AniIOT/Foldable_Robotics_Project/04_Software/05_Markdown/Gallery.md

# Gallery

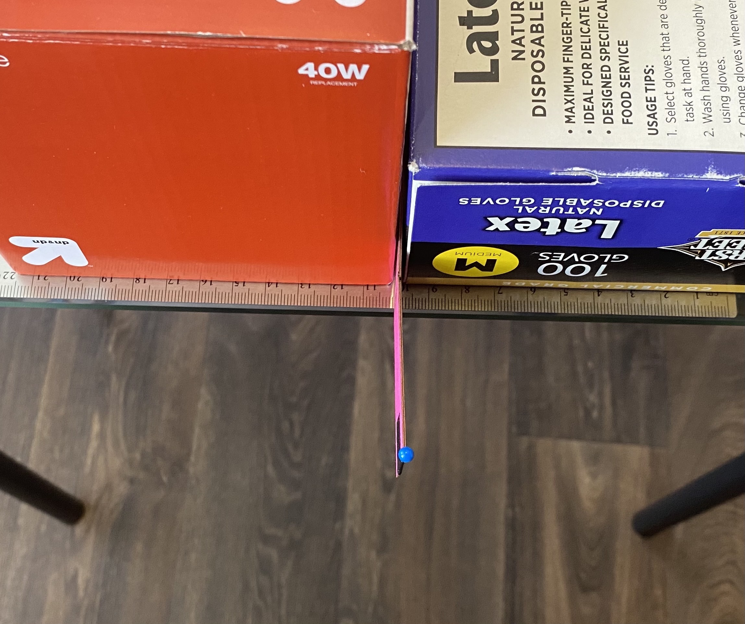
[picture p22: 04_Software/03_Anson/Damping_test_1.jpg]
damping_test_1


**Fig. 1: Damping test 1**

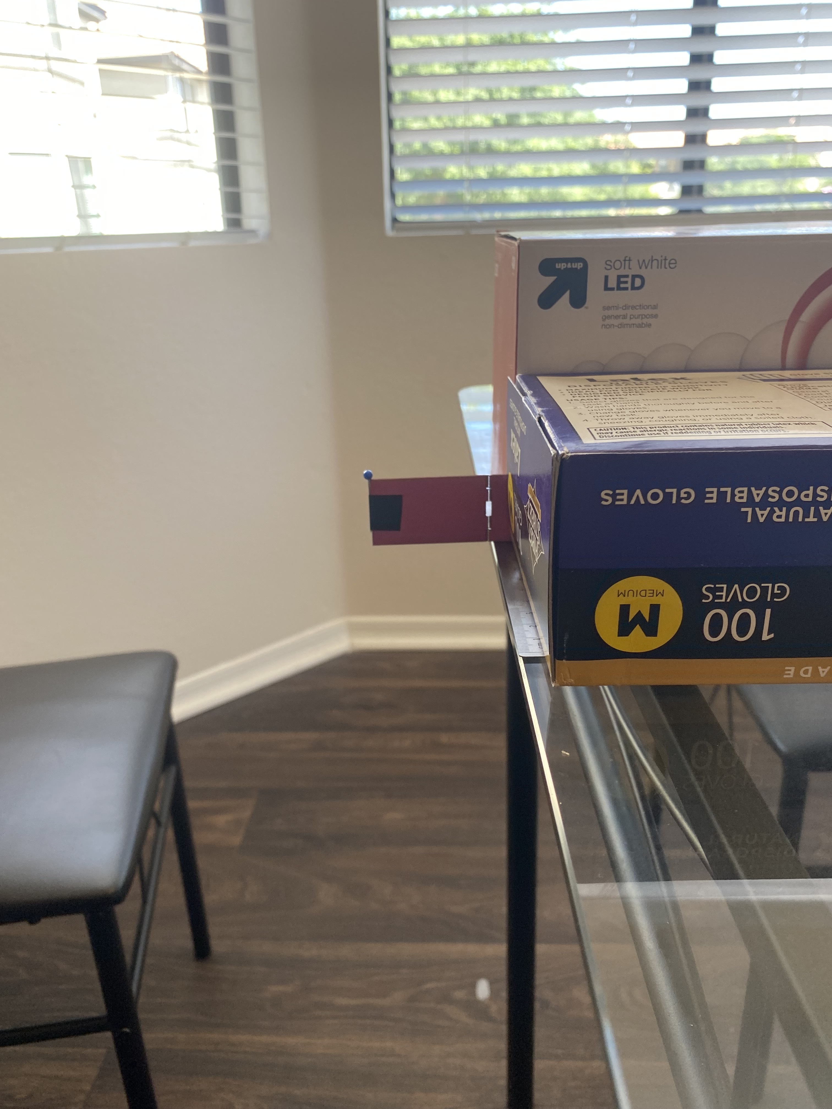
[picture p23: 04_Software/03_Anson/Damping_test_2.jpg]
damping_test_2


**Fig. 2: Damping test 2**

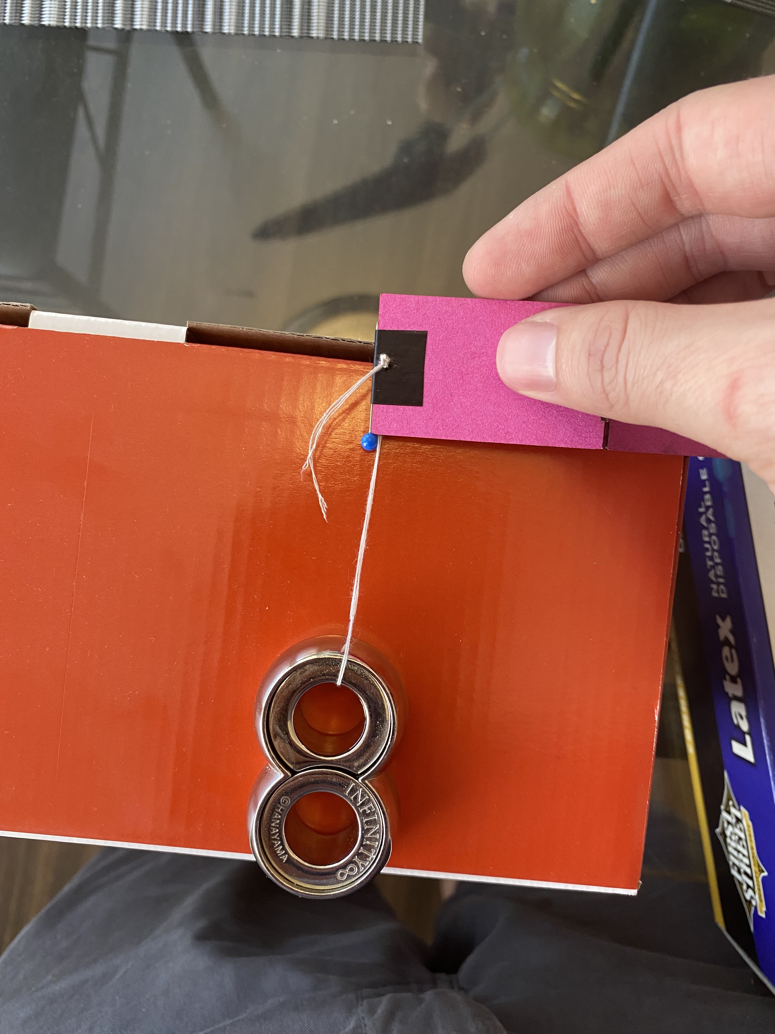
[picture p24: 04_Software/03_Anson/deflection_test1.jpg]
deflection_test_1


**Fig. 3: Deflection test 1**

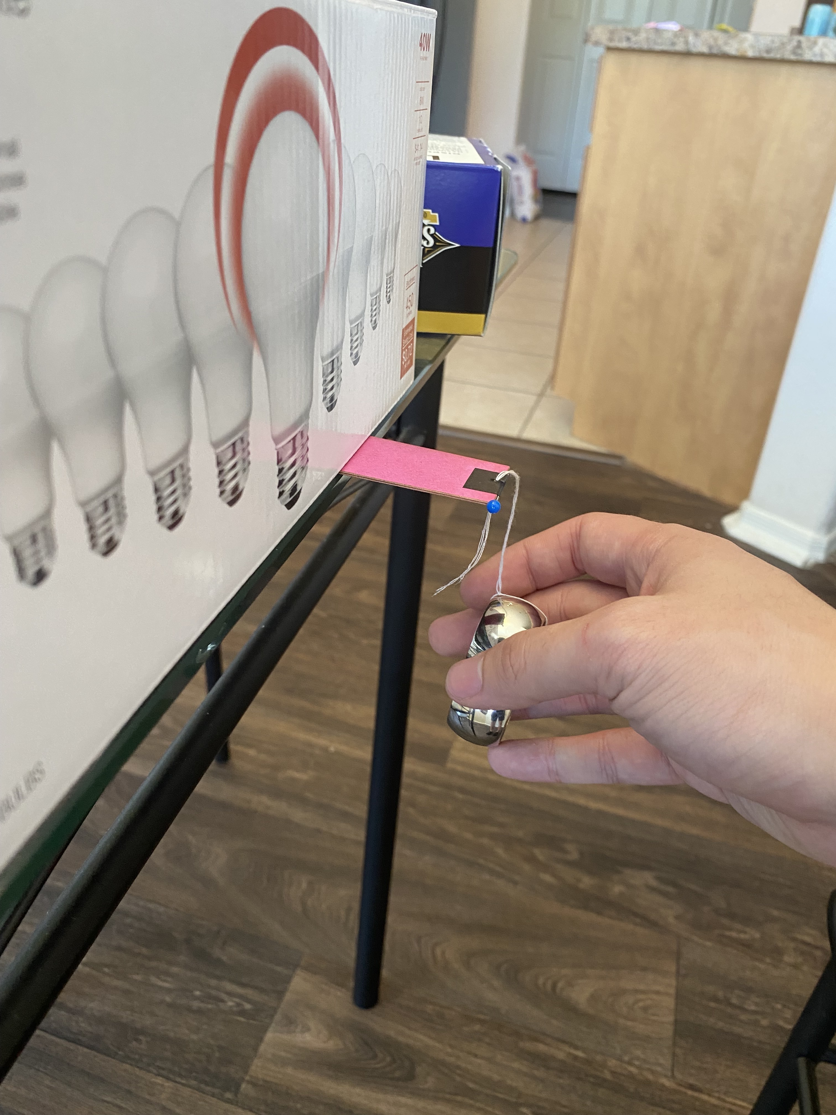
[picture p25: 04_Software/03_Anson/Deflection_test2.jpg]
deflection_test_2


**Fig. 4: Deflection test 2**

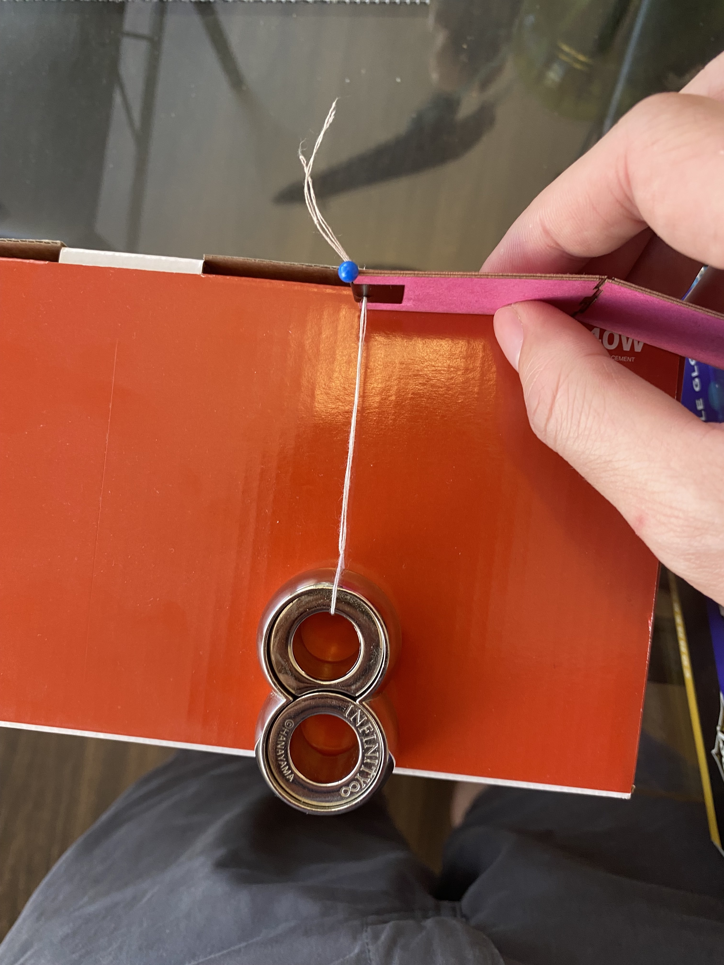
[picture p26: 04_Software/03_Anson/Deflection_test3.jpg]
deflection_test_3


**Fig. 5: Deflection test 3**

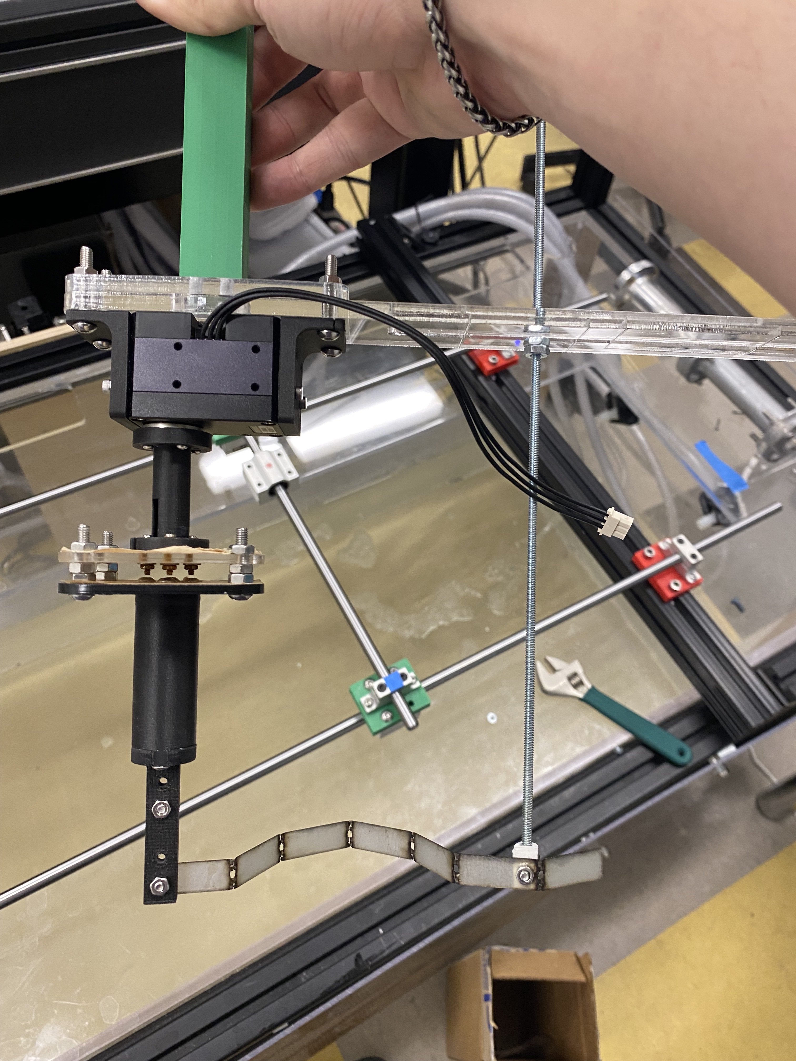
[picture p27: 04_Software/03_Anson/IMG_5635.jpg]
experimental_setup


**Fig. 6: Experimental Setup**

2D_Drawing

**Fig. 7: 2D Drawing of proposed Mechanism**

manufacturing

**Fig. 8: Remains of Manufacturing**
