AniIOT/Foldable_Robotics_Project/04_Software/05_Markdown/SystemDynamics.md

---
title: System Dyamics
---
# Dynamics I:

```python
%matplotlib inline
```

```python
#Set model to freely swim
use_free_move = False
```

# Importing Libraries

Importing libraries for script

```python
import pynamics
from pynamics.frame import Frame
from pynamics.variable_types import Differentiable,Constant
from pynamics.system import System
from pynamics.body import Body
from pynamics.dyadic import Dyadic
from pynamics.output import Output,PointsOutput
from pynamics.output_points_3d import PointsOutput3D
from pynamics.constraint import AccelerationConstraint,KinematicConstraint
from pynamics.particle import Particle
import pynamics.integration
import numpy
import matplotlib.pyplot as plt
plt.ion()
from math import pi,sin
import sympy
from sympy import sqrt
import math
import scipy.optimize
from matplotlib import animation, rc
from IPython.display import HTML

system = System()
pynamics.set_system(__name__,system)
```

# Constants of System

In this block of code we are defining all the constants of our system that we will use for our simulation

```python
#Defining Constants of System
seg_len = 0.005    #segment mass
seg_mass = 1 #segment mass 
seg_h = 1 #segment height
seg_th = 1 #segment thickness

#Set segment lengths
l = Constant(seg_len,'l',system)
lP = Constant(seg_len*5,'lP',system) #Constrained length

#Set masses
m = Constant(seg_mass,'m',system)

b = Constant(1e-1,'b',system)
k = Constant(1e-1,'k',system)
area = Constant(seg_len*seg_h,'area',system)
rho = Constant(998,'rho',system)

freq = Constant(0.2,'freq',system)
amp = Constant(30*pi/180,'amp',system)
torque = Constant(.7,'torque',system)

Ixx = Constant(1/12*seg_mass*(seg_h**2 + seg_th**2),'Ixx',system)
Iyy = Constant(1/12*seg_mass*(seg_h**2 + seg_len**2),'Iyy',system)
Izz = Constant(1/12*seg_mass*(seg_len**2 + seg_th**2),'Izz',system)

```

```python
#Set integration tolerance
tol = 1e-12
```

```python
#Set simulation run time
fps = 30
tinitial = 0
tfinal = 10
tstep = 1/fps
t = numpy.r_[tinitial:tfinal:tstep]
```

```python
#Define derivatives of frames
qA,qA_d,qA_dd = Differentiable('qA',system)
qB,qB_d,qB_dd = Differentiable('qB',system)
qC,qC_d,qC_dd = Differentiable('qC',system)
qD,qD_d,qD_dd = Differentiable('qD',system)
qE,qE_d,qE_dd = Differentiable('qE',system)
qF,qF_d,qF_dd = Differentiable('qF',system)
qG,qG_d,qG_dd = Differentiable('qG',system)

if use_free_move:
    x,x_d,x_dd = Differentiable('x',system)
    y,y_d,y_dd = Differentiable('y',system)
```

```python
#set initial conditions
initialvalues = {}
initialvalues[qA]=70*pi/180
initialvalues[qA_d]=0*pi/180
initialvalues[qB]=30*pi/180
initialvalues[qB_d]=0*pi/180
initialvalues[qC]=0*pi/180
initialvalues[qC_d]=0*pi/180
initialvalues[qD]=0*pi/180
initialvalues[qD_d]=0*pi/180
initialvalues[qE]=-10*pi/180
initialvalues[qE_d]=0*pi/180
initialvalues[qF]=-40*pi/180
initialvalues[qF_d]=0*pi/180
initialvalues[qG]=0*pi/180
initialvalues[qG_d]=0*pi/180

if use_free_move:
    initialvalues[x]=0*pi/180
    initialvalues[x_d]=0*pi/180
    initialvalues[y]=0*pi/180
    initialvalues[y_d]=0*pi/180

statevariables = system.get_state_variables()
ini0 = [initialvalues[item] for item in statevariables]
```

```python
#Frames
N = Frame('N',system)
A = Frame('A',system)
B = Frame('B',system)
C = Frame('C',system)
D = Frame('D',system)
E = Frame('E',system)
F = Frame('F',system)
G = Frame('G',system)

system.set_newtonian(N)

A.rotate_fixed_axis(N,[0,0,1],qA,system)
B.rotate_fixed_axis(N,[0,0,1],qB,system)
C.rotate_fixed_axis(N,[0,0,1],qC,system)
D.rotate_fixed_axis(N,[0,0,1],qD,system)
E.rotate_fixed_axis(N,[0,0,1],qE,system)
F.rotate_fixed_axis(N,[0,0,1],qF,system)
G.rotate_fixed_axis(N,[0,0,1],qG,system)
```

# Defining Vectors

In this section of code we are defining all the position and center of mass vecotors. Additionally we are calculating angular velocity of each frame and the respective linear velocities at the center of mass. We also build each body of the system in this section.

```python
#Vectors

if use_free_move:
    pNA=x*N.x + y*N.y + 0*N.z
    pP = lP*N.x + pNA
else:
    pNA=0*N.x + 0*N.y + 0*N.z
    pP = lP*N.x
    
pAB= pNA + l*A.x
pBC = pAB + l*B.x
pCD = pBC + l*C.x
pDE = pCD + l*D.x
pEF = pDE + l*E.x
pFG = pEF + l*F.x
pGtip = pFG + l*G.x

#Center of Mass
pAcm=pNA+l/2*A.x
pBcm=pAB+l/2*B.x
pCcm=pBC+l/2*C.x
pDcm=pCD+l/2*D.x
pEcm=pDE+l/2*E.x
pFcm=pEF+l/2*F.x
pGcm=pFG+l/2*G.x

#Angular Velocity
wNA = N.get_w_to(A)
wAB = A.get_w_to(B) 
wBC = B.get_w_to(C)
wCD = C.get_w_to(D) 
wDE = D.get_w_to(E)
wEF = E.get_w_to(F)
wFG = F.get_w_to(G)

#Velocities 
vA=pAcm.time_derivative()
vB=pBcm.time_derivative()
vC=pCcm.time_derivative()
vD=pDcm.time_derivative()
vE=pEcm.time_derivative()
vF=pFcm.time_derivative()
vGtip=pGtip.time_derivative()

#Interia and Bodys
IA = Dyadic.build(A,Ixx,Iyy,Izz)
IB = Dyadic.build(B,Ixx,Iyy,Izz)
IC = Dyadic.build(C,Ixx,Iyy,Izz)
ID = Dyadic.build(D,Ixx,Iyy,Izz)
IE = Dyadic.build(E,Ixx,Iyy,Izz)
IF = Dyadic.build(F,Ixx,Iyy,Izz)
IG = Dyadic.build(G,Ixx,Iyy,Izz)

BodyA = Body('BodyA',A,pAcm,m,IA,system)
BodyB = Body('BodyB',B,pBcm,m,IB,system)
BodyC = Body('BodyC',C,pCcm,m,IC,system)
BodyD = Body('BodyD',D,pDcm,m,ID,system)
BodyE = Body('BodyE',E,pEcm,m,IE,system)
BodyF = Body('BodyF',F,pFcm,m,IF,system)
BodyG = Body('BodyG',G,pGcm,m,IG,system)
```

# Adding Forces

In this section of code we are adding the aerodynamic, spring, and damping forces in the system. The damping and spring values will be calculated experimentally.

```python
#Forces
system.addforce(-torque*sympy.sin(freq*2*pi*system.t)*A.z,wNA) #setting motor parameter

#Aerodynamic Forces
f_aero_Ay = rho * vA.length()*(vA.dot(A.y)) * area * A.y
f_aero_By = rho * vB.length()*(vB.dot(B.y)) * area * B.y
f_aero_Cy = rho * vC.length()*(vC.dot(C.y)) * area * C.y
f_aero_Dy = rho * vD.length()*(vD.dot(D.y)) * area * D.y
f_aero_Ey = rho * vE.length()*(vE.dot(E.y)) * area * E.y
f_aero_Fy = rho * vF.length()*(vF.dot(F.y)) * area * F.y
f_aero_Gy = rho * vGtip.length()*(vGtip.dot(G.y)) * area * G.y

system.addforce(-f_aero_Ay,vA)
system.addforce(-f_aero_By,vB)
system.addforce(-f_aero_Cy,vC)
system.addforce(-f_aero_Dy,vD)
system.addforce(-f_aero_Ey,vE)
system.addforce(-f_aero_Fy,vF)
system.addforce(-f_aero_Gy,vGtip)

#Damping Forces
system.addforce(-b*wNA,wNA)
system.addforce(-b*wAB,wAB)
system.addforce(-b*wBC,wBC)
system.addforce(-b*wCD,wCD)
system.addforce(-b*wDE,wDE)
system.addforce(-b*wEF,wEF)
system.addforce(-b*5*wFG,wFG)

#Spring Force (Torsion)
system.add_spring_force1(k,(qA)*N.z,wNA) 
system.add_spring_force1(k,(qB-qA)*N.z,wAB)
system.add_spring_force1(k,(qC-qB)*N.z,wBC)
system.add_spring_force1(k,(qD-qC)*N.z,wCD) 
system.add_spring_force1(k,(qE-qD)*N.z,wDE)
system.add_spring_force1(k,(qF-qE)*N.z,wEF)
system.add_spring_force1(5*k,(qG-qF)*N.z,wFG)
```

    (<pynamics.force.Force at 0x1f6381fff40>,
     <pynamics.spring.Spring at 0x1f6381ffd90>)

# Initial Condition

Solving for initial condition constraints and using scipy to solve for initial states and setting initial states to system initial states.

```python
#Constraints for initial condition

eq = []
eq.append(pFG-pP)
    
eq_scalar = []
eq_scalar.append(eq[0].dot(N.x))
eq_scalar.append(eq[0].dot(N.y))
```

```python
#Solve for Intial Conditions
if use_free_move:
    qi = [qA,x,y]
else:  
    qi = [qA]

qd = [qB,qC,qD,qE,qF,qG]

eq_scalar_c = [item.subs(system.constant_values) for item in eq_scalar]
defined = dict([(item,initialvalues[item]) for item in qi])
eq_scalar_c = [item.subs(defined) for item in eq_scalar_c]

error = (numpy.array(eq_scalar_c)**2).sum()

f = sympy.lambdify(qd,error)

def function(args):
    return f(*args)

guess = [initialvalues[item] for item in qd]

result = scipy.optimize.minimize(function,guess)
if result.fun>1e-3:
    raise(Exception("out of tolerance"))
    
ini = []
for item in system.get_state_variables():
    if item in qd:
        ini.append(result.x[qd.index(item)])
    else:
        ini.append(initialvalues[item])
```

# Setting Dynamic Constraints

Solving for dynamic constraints of system to run simulation.

```python
#Adding Dynamic Constraints

#Position of motor limits
#pos = amp*sympy.cos(freq*2*pi*system.t)

#eq.append(pos*N.z-qA*N.z)

eq_scalar = []
eq_scalar.append(eq[0].dot(N.x))
eq_scalar.append(eq[0].dot(N.y))
#eq_scalar.append(eq[1].dot(N.z))
eq_scalar_d = [system.derivative(item) for item in eq_scalar]
eq_scalar_dd = [system.derivative(item) for item in eq_scalar_d]

system.add_constraint(AccelerationConstraint(eq_scalar_dd))

```

# Solving for Simulation

Code to run simulation and plot motion, states, and total energy in system.

```python
#Solve model and plot angles

f,ma = system.getdynamics()

func1,lambda1 = system.state_space_post_invert(f,ma,return_lambda = True)

states=pynamics.integration.integrate(func1,ini,t,rtol=tol,atol=tol,hmin=tol, args=({'constants':system.constant_values},))

plt.figure()
artists = plt.plot(t,states[:,:7])
plt.legend(artists,['qA','qB','qC','qD','qE','qF','qG'])
```

    2022-04-08 21:14:54,467 - pynamics.system - INFO - getting dynamic equations
    2022-04-08 21:14:59,173 - pynamics.system - INFO - solving a = f/m and creating function
    2022-04-08 21:15:07,435 - pynamics.system - INFO - substituting constrained in Ma-f.
    2022-04-08 21:15:09,758 - pynamics.system - INFO - done solving a = f/m and creating function
    2022-04-08 21:15:09,758 - pynamics.system - INFO - calculating function for lambdas
    2022-04-08 21:15:09,823 - pynamics.integration - INFO - beginning integration
    2022-04-08 21:15:09,823 - pynamics.system - INFO - integration at time 0000.00
    2022-04-08 21:15:25,619 - pynamics.system - INFO - integration at time 0004.49
    2022-04-08 21:15:39,694 - pynamics.system - INFO - integration at time 0009.61
    2022-04-08 21:15:40,691 - pynamics.integration - INFO - finished integration

    <matplotlib.legend.Legend at 0x1f63a3cc7c0>

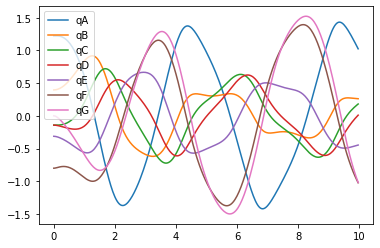
[picture p28: 01_Documents/04_Presentations/System_Dynamics/Dynamics_1/output_21_2.png]


```python
points = [pNA,pAB,pBC,pCD,pDE,pEF,pFG,pGtip]
points_output = PointsOutput(points,system)
y = points_output.calc(states,t)
points_output.plot_time(20)
```

    2022-04-08 21:15:41,385 - pynamics.output - INFO - calculating outputs
    2022-04-08 21:15:41,426 - pynamics.output - INFO - done calculating outputs

    <AxesSubplot:>

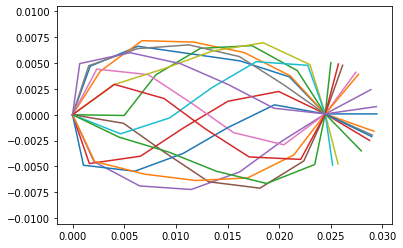
[picture p29: 01_Documents/04_Presentations/System_Dynamics/Dynamics_1/output_22_2.png]


```python
#Constraint Forces

lambda2 = numpy.array([lambda1(item1,item2,system.constant_values) for item1,item2 in zip(t,states)])
plt.figure()
plt.plot(t, lambda2)
```

    [<matplotlib.lines.Line2D at 0x1f63a62ea30>,
     <matplotlib.lines.Line2D at 0x1f63a62ea90>]

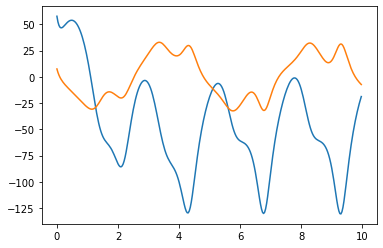
[picture p30: 01_Documents/04_Presentations/System_Dynamics/Dynamics_1/output_23_1.png]


```python
#Energy Plot

KE = system.get_KE()
PE = system.getPESprings()
energy_output = Output([KE-PE],system)
energy_output.calc(states,t)
energy_output.plot_time(t)
```

    2022-04-08 21:15:46,679 - pynamics.output - INFO - calculating outputs
    2022-04-08 21:15:46,855 - pynamics.output - INFO - done calculating outputs

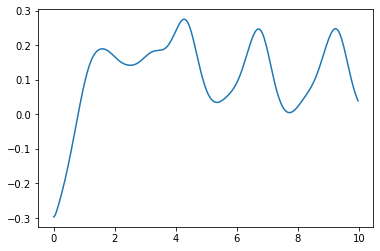
[picture p31: 01_Documents/04_Presentations/System_Dynamics/Dynamics_1/output_24_1.png]


```python
#Plotting Motion of Tail

plt.plot(y[:,7,0],y[:,7,1])
plt.axis('equal')
plt.title('Position of Tail')
plt.xlabel('Position X (m)')
plt.ylabel('Position Y (m)')
```

    Text(0, 0.5, 'Position Y (m)')

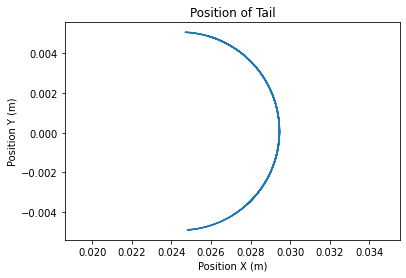
[picture p32: 01_Documents/04_Presentations/System_Dynamics/Dynamics_1/output_25_1.png]


```python
if use_free_move:
    points_output.animate(fps = fps,movie_name = 'dynamics_free_swimming.mp4',lw=2,marker='o',color=(1,0,0,1),linestyle='-')
else:
    points_output.animate(fps = fps,movie_name = 'dynamics.mp4',lw=2,marker='o',color=(1,0,0,1),linestyle='-')
    
HTML(points_output.anim.to_html5_video())
```

<video width="432" height="288" controls autoplay loop>
  <source type="video/mp4" src="data:video/mp4;base64,AAAAIGZ0eXBNNFYgAAACAE00ViBpc29taXNvMmF2YzEAAAAIZnJlZQACGGRtZGF0AAACoAYF//+c
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
AAEAAAAATGF2ZjU4LjQ1LjEwMA==
">
  Your browser does not support the video tag.
</video>

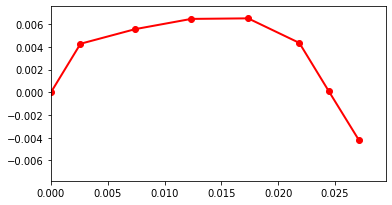
[picture p33: 01_Documents/04_Presentations/System_Dynamics/Dynamics_1/output_26_1.png]


# Parameter Identification Plan:

1. Identify and discuss the materials you plan to use in fabrication. Decide who will be obtaining those materials and distributing them.
* For the flexible core, polyester will be used
*  For the stiff segments, stiff card stock of one or two layers will be used.
* The stiff frame of the robot will be 3D printed from PLA.
    * The frame is a stiff segment of plastic that attaches the actuator to the first segment of the robot and secures the two hinge pins in place. 
* The hinge pin will be made from a metal wire/rod
* Jacob Yoshitake will be responsible for obtaining the materials and distributing them.

2. Identify and discuss the various parameters you plan to model in your simulation.  Discuss your plans for experimentally obtaining each of those values, and the model you would like to use for describing each phenomenon.
* Actuator Modeling
    * We need to determine the torque generated and verify the position output of the servo used for the device. This is critical to matching up the simulation and physical device for position based control. We will measure the current and voltage and measure the output of the position of the servo horn to verify the torque generated by the servo.

* Link Stiffness
    * We need to verify that the links used for the device can be assumed as a rigid body and does not require any additional spring and damping representation to model the links. We will do this by measuring the deflection of the link to calculate the stiffness of the link.

* Joint stiffness and damping
    * Tuning the spring and damping constants is crucial for this project because it will determine how the wave will traverse through the body. This will be done through modeling a two link system to isolate a singular joint. The data that we will be collecting is the position data of the two link pendulum and fitting the simulation to the data.

* Mass and Inertia
    * We will model the links in SolidWorks to generate the inertial values of the link. In order to get this information, we will need to measure the mass and dimensions of the link.

3. Identify and discuss how you plan to prototype your system and assign one person to do that
* Jacob Yoshitake will be in charge of prototyping.
* The polyester and stiff card stock will be cut using the laser cutter in the innovation hub, then laminated together.
* The stiff spine of the robot will be 3D printed and the pins will be made of a thin metal rod.
* If additional stiffness is needed for the system, additional layers of card stock or 3D printed frames can be added to the final design.

4. Identify and discuss how you plan to collect system-level motion or force data, including
* Method (IMU, video, discrete joint sensors, force/torque sensing)
    * In order to capture the system-level motion, the team will be video recording the foldable device to collect the data.
* Data extraction approach
    * We will be using the video to map the segments at different points, and compare it to the voltage of the system. Based on the voltage at the certain points and the torque of the servo motor, we will calculate the forces at each segment.

5. Identify and discuss your plan for shared simulation tasks
* Anson Kwan and Aniruddha Anand Damle will take the task of updating the code
* The data obtained from the experiments will be used to compare and reduce the error between the simulation and the actual experiment.
* We will determine the filtering and interpolation algorithm after we collect the data. Other preprocessing can also be done after the data has been collected.

6. Finally, identify and discuss any reporting tasks that may be needed
* Data Collection
* Design and manufacturing workflow
* Parameter identification
* Prototyping
* Presentation II
* Optimization and Analysis
* Presentation III

# Individual Parameter ID:

<data>
<table>
    <tr>
        <th>Tasks</th>
        <th>Aniruddha</th>
        <th>Anson</th>
        <th>Bryan</th>
        <th>Jacob</th>
    </tr>
    <tr>
        <th>Link Stiffness</th>
        <td></td>
        <td style = "background-color:#6FFB06"></td>
        <td style = "background-color:#6FFB06"></td>
        <td></td>
    </tr>
    <tr>
        <th>Joint Stiffness and Damping</th>
        <td style = "background-color:#6FFB06"></td>
        <td style = "background-color:#6FFB06"></td>
        <td style = "background-color:#6FFB06"></td>
        <td style = "background-color:#6FFB06"></td>
    </tr>
    <tr>
        <th>Mass and Inertia</th>
        <td style = "background-color:#6FFB06"></td>
        <td></td>
        <td></td>
        <td></td>
    </tr>
    <tr>
        <th>Actuator Modeling</th>
        <td></td>
        <td></td>
        <td></td>
        <td style = "background-color:#6FFB06"></td>
    </tr>
    <tr>
        <th>Code</th>
        <td style = "background-color:#6FFB06"></td>
        <td style = "background-color:#6FFB06"></td>
        <td></td>
        <td></td>
    </tr>
    <tr>
        <th>Prototyping</th>
        <td></td>
        <td></td>
        <td style = "background-color:#6FFB06"></td>
        <td style = "background-color:#6FFB06"></td>
    </tr>
</table>
</data>

# Dynamics II:
```python
%matplotlib inline
```

```python
#Set model to freely swim
use_free_move = True
```

# Importing Libraries

Importing libraries for script

```python
import pynamics
from pynamics.frame import Frame
from pynamics.variable_types import Differentiable,Constant
from pynamics.system import System
from pynamics.body import Body
from pynamics.dyadic import Dyadic
from pynamics.output import Output,PointsOutput
from pynamics.output_points_3d import PointsOutput3D
from pynamics.constraint import AccelerationConstraint,KinematicConstraint
from pynamics.particle import Particle
import pynamics.integration
import numpy
import matplotlib.pyplot as plt
plt.ion()
from math import pi,sin
import sympy
from sympy import sqrt
import math
import scipy.optimize
from matplotlib import animation, rc
from IPython.display import HTML

system = System()
pynamics.set_system(__name__,system)
```

# Constants of System

In this block of code we are defining all the constants of our system that we will use for our simulation

```python
#Defining Constants of System
seg_len = 0.03    #segment mass
seg_mass = 1 #segment mass 
seg_h = 0.04 #segment height

#Set segment lengths
lA = Constant(seg_len,'lA',system)
lB = Constant(seg_len,'lB',system)
lC = Constant(seg_len,'lC',system)
lD = Constant(seg_len,'lD',system)
lE = Constant(seg_len,'lE',system)
lF = Constant(seg_len,'lF',system)
lG = Constant(seg_len,'tail',system)
lP = Constant(seg_len*5.5,'lP',system) #Constrained length

#Set masses
mA = Constant(seg_mass,'mA',system)
mB = Constant(seg_mass,'mB',system)
mC = Constant(seg_mass,'mC',system)
mD = Constant(seg_mass,'mD',system)
mE = Constant(seg_mass,'mE',system)
mF = Constant(seg_mass,'mF',system)
mG = Constant(seg_mass,'mG',system)

b = Constant(1e-1,'b',system)
k = Constant(1e0,'k',system)
area = Constant(seg_len*seg_h,'area',system)
rho = Constant(998,'rho',system)

freq = Constant(.5,'freq',system)
amp = Constant(40*pi/180,'amp',system)
torque = Constant(.7,'torque',system)

Ixx = Constant(1/12*seg_mass*(seg_h*2),'Ixx',system)
Iyy = Constant(1/12*seg_mass*(seg_h**2 + seg_len**2),'Iyy',system)
Izz = Constant(1/12*seg_mass*(seg_len**2),'Izz',system)
Ixx_G = Constant(1/12*seg_mass*(seg_h*2),'Ixx_G',system)
Iyy_G = Constant(1/12*seg_mass*(seg_h**2 + seg_len**2),'Iyy_G',system)
Izz_G = Constant(1/12*seg_mass*(seg_len**2),'Izz_G',system)

```

```python
#Set integration tolerance
tol = 1e-12
```

```python
#Set simulation run time
fps = 30
tinitial = 0
tfinal = 10
tstep = 1/fps
t = numpy.r_[tinitial:tfinal:tstep]
```

```python
#Define derivatives of frames
qA,qA_d,qA_dd = Differentiable('qA',system)
qB,qB_d,qB_dd = Differentiable('qB',system)
qC,qC_d,qC_dd = Differentiable('qC',system)
qD,qD_d,qD_dd = Differentiable('qD',system)
qE,qE_d,qE_dd = Differentiable('qE',system)
qF,qF_d,qF_dd = Differentiable('qF',system)
qG,qG_d,qG_dd = Differentiable('qG',system)

if use_free_move:
    x,x_d,x_dd = Differentiable('x',system)
    y,y_d,y_dd = Differentiable('y',system)
```

```python
#set initial conditions
initialvalues = {}
initialvalues[qA]=40*pi/180
initialvalues[qA_d]=0*pi/180
initialvalues[qB]=20*pi/180
initialvalues[qB_d]=0*pi/180
initialvalues[qC]=10*pi/180
initialvalues[qC_d]=0*pi/180
initialvalues[qD]=0*pi/180
initialvalues[qD_d]=0*pi/180
initialvalues[qE]=-10*pi/180
initialvalues[qE_d]=0*pi/180
initialvalues[qF]=-40*pi/180
initialvalues[qF_d]=0*pi/180
initialvalues[qG]=-40*pi/180
initialvalues[qG_d]=0*pi/180

if use_free_move:
    initialvalues[x]=0*pi/180
    initialvalues[x_d]=0*pi/180
    initialvalues[y]=0*pi/180
    initialvalues[y_d]=0*pi/180

statevariables = system.get_state_variables()
ini0 = [initialvalues[item] for item in statevariables]
```

```python
#Frames
N = Frame('N',system)
A = Frame('A',system)
B = Frame('B',system)
C = Frame('C',system)
D = Frame('D',system)
E = Frame('E',system)
F = Frame('F',system)
G = Frame('G',system)

system.set_newtonian(N)

A.rotate_fixed_axis(N,[0,0,1],qA,system)
B.rotate_fixed_axis(N,[0,0,1],qB,system)
C.rotate_fixed_axis(N,[0,0,1],qC,system)
D.rotate_fixed_axis(N,[0,0,1],qD,system)
E.rotate_fixed_axis(N,[0,0,1],qE,system)
F.rotate_fixed_axis(N,[0,0,1],qF,system)
G.rotate_fixed_axis(N,[0,0,1],qG,system)
```

# Defining Vectors

In this section of code we are defining all the position and center of mass vecotors. Additionally we are calculating angular velocity of each frame and the respective linear velocities at the center of mass. We also build each body of the system in this section.

```python
#Vectors
if use_free_move:
    pNA=x*N.x + y*N.y + 0*N.z
    pP = lP*N.x + pNA
else:
    pNA=0*N.x + 0*N.y + 0*N.z
    pP = lP*N.x
    
pAB= pNA + lA*A.x
pBC = pAB + lB*B.x
pCD = pBC + lC*C.x
pDE = pCD + lD*D.x
pEF = pDE + lE*E.x
pFG = pEF + lF*F.x
pGtip = pFG + lG*G.x

#Center of Mass
pAcm=pNA+lA/2*A.x
pBcm=pAB+lB/2*B.x
pCcm=pBC+lC/2*C.x
pDcm=pCD+lD/2*D.x
pEcm=pDE+lE/2*E.x
pFcm=pEF+lF/2*F.x
pGcm=pFG+lG/2*G.x

#Angular Velocity
wNA = N.get_w_to(A)
wAB = A.get_w_to(B) 
wBC = B.get_w_to(C)
wCD = C.get_w_to(D) 
wDE = D.get_w_to(E)
wEF = E.get_w_to(F)
wFG = F.get_w_to(G)

#Velocities 
vA=pAcm.time_derivative()
vB=pBcm.time_derivative()
vC=pCcm.time_derivative()
vD=pDcm.time_derivative()
vE=pEcm.time_derivative()
vF=pFcm.time_derivative()
vGtip=pGtip.time_derivative()

#Interia and Bodys
IA = Dyadic.build(A,Ixx,Iyy,Izz)
IB = Dyadic.build(B,Ixx,Iyy,Izz)
IC = Dyadic.build(C,Ixx,Iyy,Izz)
ID = Dyadic.build(D,Ixx,Iyy,Izz)
IE = Dyadic.build(E,Ixx,Iyy,Izz)
IF = Dyadic.build(F,Ixx,Iyy,Izz)
IG = Dyadic.build(G,Ixx_G,Iyy_G,Izz_G)

BodyA = Body('BodyA',A,pAcm,mA,IA,system)
BodyB = Body('BodyB',B,pBcm,mB,IB,system)
BodyC = Body('BodyC',C,pCcm,mC,IC,system)
BodyD = Body('BodyD',D,pDcm,mD,ID,system)
BodyE = Body('BodyE',E,pEcm,mE,IE,system)
BodyF = Body('BodyF',F,pFcm,mF,IF,system)
BodyG = Body('BodyG',G,pGcm,mG,IG,system)
```

# Adding Forces

In this section of code we are adding the aerodynamic, spring, and damping forces in the system. The damping and spring values will be calculated experimentally.

```python
#Forces
#system.addforce(-torque*sympy.sin(freq*2*pi*system.t)*A.z,wNA) #setting motor parameter

#Aerodynamic Forces
f_aero_Ay = rho * vA.length()*(vA.dot(A.y)) * area * A.y
f_aero_By = rho * vB.length()*(vB.dot(B.y)) * area * B.y
f_aero_Cy = rho * vC.length()*(vC.dot(C.y)) * area * C.y
f_aero_Dy = rho * vD.length()*(vD.dot(D.y)) * area * D.y
f_aero_Ey = rho * vE.length()*(vE.dot(E.y)) * area * E.y
f_aero_Fy = rho * vF.length()*(vF.dot(F.y)) * area * F.y
f_aero_Gy = rho * vGtip.length()*(vGtip.dot(G.y)) * area * G.y

system.addforce(-f_aero_Ay,vA)
system.addforce(-f_aero_By,vB)
system.addforce(-f_aero_Cy,vC)
system.addforce(-f_aero_Dy,vD)
system.addforce(-f_aero_Ey,vE)
system.addforce(-f_aero_Fy,vF)
system.addforce(-f_aero_Gy,vGtip)

#Damping Forces
system.addforce(-b*wNA,wNA)
system.addforce(-b*wAB,wAB)
system.addforce(-b*wBC,wBC)
system.addforce(-b*wCD,wCD)
system.addforce(-b*wDE,wDE)
system.addforce(-b*wEF,wEF)
system.addforce(-b*wFG,wFG)

#Spring Force (Torsion)
system.add_spring_force1(k,(qA)*N.z,wNA) 
system.add_spring_force1(k,(qB-qA)*N.z,wAB)
system.add_spring_force1(k,(qC-qB)*N.z,wBC)
system.add_spring_force1(k,(qD-qC)*N.z,wCD) 
system.add_spring_force1(k,(qE-qD)*N.z,wDE)
system.add_spring_force1(k,(qF-qE)*N.z,wEF)
system.add_spring_force1(k,(qG-qF)*N.z,wFG)
```

    (<pynamics.force.Force at 0x1df9f3a3640>,
     <pynamics.spring.Spring at 0x1df9f3a3760>)

# Initial Condition

Solving for initial condition constraints and using scipy to solve for initial states and setting initial states to system initial states.

```python
#Constraints for initial condition

eq = []

eq.append(pFG-pP)
    
eq_scalar = []
eq_scalar.append(eq[0].dot(N.x))
eq_scalar.append(eq[0].dot(N.y))

#system.add_constraint(KinematicConstraint(eq_scalar))
```

```python
#Solve for Intial Conditions
if use_free_move:
    qi = [qA,x,y]
else:  
    qi = [qA]

qd = [qB,qC,qD,qE,qF,qG]

eq_scalar_c = [item.subs(system.constant_values) for item in eq_scalar]
defined = dict([(item,initialvalues[item]) for item in qi])
eq_scalar_c = [item.subs(defined) for item in eq_scalar_c]

error = (numpy.array(eq_scalar_c)**2).sum()

f = sympy.lambdify(qd,error)

def function(args):
    return f(*args)

guess = [initialvalues[item] for item in qd]

result = scipy.optimize.minimize(function,guess)
if result.fun>1e-3:
    raise(Exception("out of tolerance"))
    
ini = []
for item in system.get_state_variables():
    if item in qd:
        ini.append(result.x[qd.index(item)])
    else:
        ini.append(initialvalues[item])
```

```python
#Plot Initial State
points = [pNA,pAB,pBC,pCD,pDE,pEF,pFG,pGtip]
points_output = PointsOutput(points, constant_values=system.constant_values)
points_output.calc(numpy.array([ini0,ini]),numpy.array([0,1]))
points_output.plot_time()
```

    2022-04-08 21:29:57,012 - pynamics.output - INFO - calculating outputs
    2022-04-08 21:29:57,020 - pynamics.output - INFO - done calculating outputs

    <AxesSubplot:>

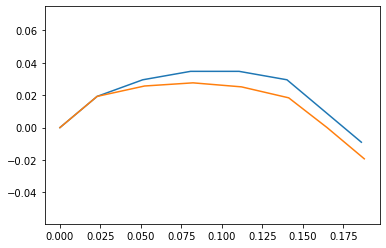
[picture p34: 01_Documents/04_Presentations/System_Dynamics/Dynamics_2/output_18_2.png]


# Setting Dynamic Constraints

Solving for dynamic constraints of system to run simulation.

```python
#Adding Dynamic Constraints

#Position of motor limits
pos = amp*sympy.cos(freq*2*pi*system.t)

eq = []

eq.append(pFG-pP)
eq.append(pos*N.z-qA*A.z)

eq_d = []
eq_d = [item.time_derivative() for item in eq]

eq_dd = []
eq_dd = [item.time_derivative() for item in eq_d]

eq_dd_scalar = []
eq_dd_scalar.append(eq_dd[0].dot(N.x))
eq_dd_scalar.append(eq_dd[0].dot(N.y))
eq_dd_scalar.append(eq_dd[1].dot(N.z))

system.add_constraint(AccelerationConstraint(eq_dd_scalar))
```

# Solving for Simulation

Code to run simulation and plot motion, states, and total energy in system.

```python
#Solve model and plot angles

f,ma = system.getdynamics()

func1,lambda1 = system.state_space_post_invert(f,ma,return_lambda = True)

states=pynamics.integration.integrate(func1,ini,t,rtol=tol,atol=tol,hmin=tol, args=({'constants':system.constant_values},))

plt.figure()
artists = plt.plot(t,states[:,:7])
plt.legend(artists,['qA','qB','qC','qD','qE','qF','qG'])
```

    2022-04-08 21:29:57,796 - pynamics.system - INFO - getting dynamic equations
    2022-04-08 21:30:04,614 - pynamics.system - INFO - solving a = f/m and creating function
    2022-04-08 21:30:19,255 - pynamics.system - INFO - substituting constrained in Ma-f.
    2022-04-08 21:30:23,118 - pynamics.system - INFO - done solving a = f/m and creating function
    2022-04-08 21:30:23,118 - pynamics.system - INFO - calculating function for lambdas
    2022-04-08 21:30:23,166 - pynamics.integration - INFO - beginning integration
    2022-04-08 21:30:23,166 - pynamics.system - INFO - integration at time 0000.00
    2022-04-08 21:30:45,434 - pynamics.system - INFO - integration at time 0000.04
    2022-04-08 21:31:05,362 - pynamics.system - INFO - integration at time 0000.40
    2022-04-08 21:31:24,753 - pynamics.system - INFO - integration at time 0001.03
    2022-04-08 21:31:44,299 - pynamics.system - INFO - integration at time 0001.18
    2022-04-08 21:32:08,280 - pynamics.system - INFO - integration at time 0001.38
    2022-04-08 21:32:30,560 - pynamics.system - INFO - integration at time 0001.96
    2022-04-08 21:32:52,474 - pynamics.system - INFO - integration at time 0002.16
    2022-04-08 21:33:14,340 - pynamics.system - INFO - integration at time 0002.32
    2022-04-08 21:33:34,077 - pynamics.system - INFO - integration at time 0002.90
    2022-04-08 21:33:53,537 - pynamics.system - INFO - integration at time 0003.14
    2022-04-08 21:34:13,608 - pynamics.system - INFO - integration at time 0003.29
    2022-04-08 21:34:35,500 - pynamics.system - INFO - integration at time 0003.84
    2022-04-08 21:34:59,809 - pynamics.system - INFO - integration at time 0004.13
    2022-04-08 21:35:24,031 - pynamics.system - INFO - integration at time 0004.25
    2022-04-08 21:35:45,771 - pynamics.system - INFO - integration at time 0004.70
    2022-04-08 21:36:07,537 - pynamics.system - INFO - integration at time 0005.09
    2022-04-08 21:36:27,456 - pynamics.system - INFO - integration at time 0005.22
    2022-04-08 21:36:46,904 - pynamics.system - INFO - integration at time 0005.60
    2022-04-08 21:37:11,341 - pynamics.system - INFO - integration at time 0006.07
    2022-04-08 21:37:35,038 - pynamics.system - INFO - integration at time 0006.20
    2022-04-08 21:37:56,928 - pynamics.system - INFO - integration at time 0006.49
    2022-04-08 21:38:25,067 - pynamics.system - INFO - integration at time 0007.03
    2022-04-08 21:38:52,523 - pynamics.system - INFO - integration at time 0007.18
    2022-04-08 21:39:15,563 - pynamics.system - INFO - integration at time 0007.37
    2022-04-08 21:39:38,602 - pynamics.system - INFO - integration at time 0007.94
    2022-04-08 21:39:59,282 - pynamics.system - INFO - integration at time 0008.15
    2022-04-08 21:40:21,976 - pynamics.system - INFO - integration at time 0008.30
    2022-04-08 21:40:44,376 - pynamics.system - INFO - integration at time 0008.86
    2022-04-08 21:41:07,836 - pynamics.system - INFO - integration at time 0009.14
    2022-04-08 21:41:30,670 - pynamics.system - INFO - integration at time 0009.26
    2022-04-08 21:41:52,442 - pynamics.system - INFO - integration at time 0009.71
    2022-04-08 21:42:04,806 - pynamics.integration - INFO - finished integration

    <matplotlib.legend.Legend at 0x1dfa1717160>

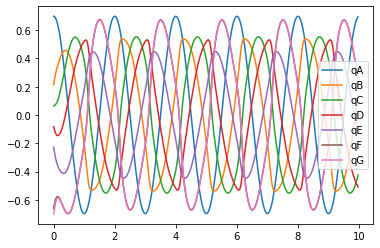
[picture p35: 01_Documents/04_Presentations/System_Dynamics/Dynamics_2/output_22_2.png]


```python
points = [pNA,pAB,pBC,pCD,pDE,pEF,pFG,pGtip]
points_output = PointsOutput(points,system)
y = points_output.calc(states,t)
points_output.plot_time(20)
```

    2022-04-08 21:42:06,037 - pynamics.output - INFO - calculating outputs
    2022-04-08 21:42:06,144 - pynamics.output - INFO - done calculating outputs

    <AxesSubplot:>

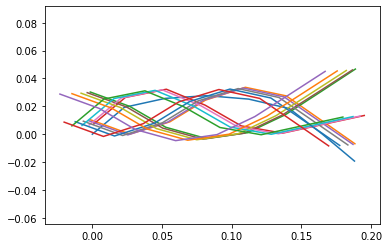
[picture p36: 01_Documents/04_Presentations/System_Dynamics/Dynamics_2/output_23_2.png]


```python
#Constraint Forces

lambda2 = numpy.array([lambda1(item1,item2,system.constant_values) for item1,item2 in zip(t,states)])
plt.figure()
plt.plot(t, lambda2)
```

    [<matplotlib.lines.Line2D at 0x1dfa1897d30>,
     <matplotlib.lines.Line2D at 0x1dfa1897d90>,
     <matplotlib.lines.Line2D at 0x1dfa1897eb0>]

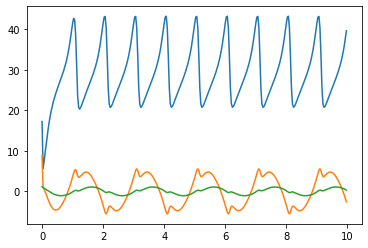
[picture p37: 01_Documents/04_Presentations/System_Dynamics/Dynamics_2/output_24_1.png]


```python
#Energy Plot

KE = system.get_KE()
PE = system.getPESprings()
energy_output = Output([KE-PE],system)
energy_output.calc(states,t)
energy_output.plot_time(t)
```

    2022-04-08 21:42:14,796 - pynamics.output - INFO - calculating outputs
    2022-04-08 21:42:15,016 - pynamics.output - INFO - done calculating outputs

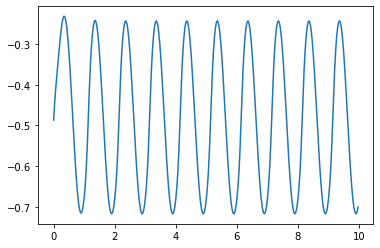
[picture p38: 01_Documents/04_Presentations/System_Dynamics/Dynamics_2/output_25_1.png]


```python
#Plotting Motion of Tail

plt.plot(y[:,7,0],y[:,7,1])
plt.axis('equal')
plt.title('Position of Tail')
plt.xlabel('Position X (m)')
plt.ylabel('Position Y (m)')
```

    Text(0, 0.5, 'Position Y (m)')

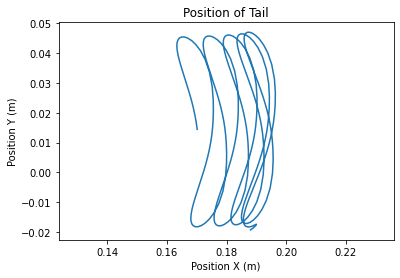
[picture p39: 01_Documents/04_Presentations/System_Dynamics/Dynamics_2/output_26_1.png]


```python
if use_free_move:
    points_output.animate(fps = fps,movie_name = 'dynamics_free_swimming.mp4',lw=2,marker='o',color=(1,0,0,1),linestyle='-')
else:
    points_output.animate(fps = fps,movie_name = 'dynamics.mp4',lw=2,marker='o',color=(1,0,0,1),linestyle='-')
    
HTML(points_output.anim.to_html5_video())
```
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
