AniIOT/Foldable_Robotics_Project/04_Software/04_Aniruddha/Frequency_optimization.pdf

## Frequency_optimization

April 27, 2022

## 1 Importing Libraries

Importing libraries for script

[3]: import pynamics
from pynamics.frame import Frame
from pynamics.variable_types import Differentiable,Constant from pynamics.system import System
from pynamics.body import Body
from pynamics.dyadic import Dyadic
from pynamics.output import Output,PointsOutput
from pynamics.output_points_3d import PointsOutput3D
from pynamics.constraint import AccelerationConstraint,KinematicConstraint from pynamics.particle import Particle
import pynamics.integration
import numpy
import matplotlib.pyplot as plt plt.ion()
from math import pi,sin
import sympy
from sympy import sqrt
import math
import logging
import scipy.optimize
import pynamics.integration import pynamics.system
import numpy.random
import scipy.interpolate
import scipy.optimize
import cma
import pandas as pd
import idealab_tools.units from matplotlib import animation, rc from IPython.display import HTML

system = System()
pynamics.set_system(__name__,system)

## 2 Constants of System

In this block of code we are defining all the constants of our system that we will use for our simulation

[4]: #seg = segment, t = tail
seg_l = 0.02
t_l = 0.02
seg_h = 0.01
len_factor = 5.5

#Set segment lengths

l = Constant(seg_l,'l',system) #Segment Length, Formula:seg_len
lT = Constant(seg_l,'tail',system) #Tail Length, Formula:tail_len
lP = Constant(seg_l*len_factor,'lP',system) #Constrained length, Forumla: ,→seg_len*constrainted_length_factor

#Set masses, 666.7 is density of laminate structure

m = Constant(666.7*seg_l*seg_h*0.001,'m',system) #Segment Mass, Formula:666. ,→7*seg_len*seg_h*seg_th
mT = Constant(666.7*t_l*seg_h*0.001,'mT',system) #Tail Mass, Formula:666. ,→7*tail_len*seg_h*seg_th

b = Constant(2.148e-6,'b',system)
k = Constant(1.599e-4,'k',system)
rho = Constant(998,'rho',system)
area_p = Constant(seg_l*seg_h,'area_p',system) #area of flat plates area_f = Constant(seg_h*0.001,'area_f',system)

freq = Constant(1,'freq',system) #frequency of head oscilation
amp = Constant(40*pi/180,'amp',system) #maximum pitch angle of servo

Ixx = Constant(1/12*(666.7*seg_l*seg_h*0.001)*(seg_h**2 + 0. ,→001**2),'Ixx',system) #Formula: 1/12*666.7*seg_len*seg_h*seg_th*(seg_h**2 +␣ ,→seg_th**2
Iyy = Constant(1/12*(666.7*seg_l*seg_h*0.001)*(seg_h**2 +␣ ,→seg_l**2),'Iyy',system) #Formula: 1/12*(666. ,→7*seg_len*seg_h*seg_th)*(seg_h**2 + seg_len**2)

Izz = Constant(1/12*(666.7*seg_l*seg_h*0.001)*(seg_l**2 + 0. ,→001**2),'Izz',system) #Formula: 1/12*(666. ,→7*seg_len*seg_h*seg_th)*(seg_len**2 + seg_th**2)
Ixx_T = Constant(1/12*(666.7*t_l*seg_h*0.001)*(seg_h*2 + 0. ,→001**2),'Ixx_T',system) #Formula: 1/12*(666. ,→7*tail_len*seg_h*seg_th)*(seg_h*2 + seg_th**2)
Iyy_T = Constant(1/12*(666.7*t_l*seg_h*0.001)*(seg_h**2 +␣ ,→t_l**2),'Iyy_T',system) #Formula: 1/12*(666. ,→7*tail_len*seg_h*seg_th)*(seg_h**2 + tail_len**2) Izz_T = Constant(1/12*(666.7*t_l*seg_h*0.001)*(t_l**2 + 0. ,→001**2),'Izz_T',system) #Formula: 1/12*(666. ,→7*tail_len*seg_h*seg_th)*(tail_len**2 + seg_th**2)

[5]: #Set integration tolerance
tol = 1e-12

[6]: #Set simulation run time fps = 30
tinitial = 0
tfinal = 2
tstep = 1/fps
t = numpy.r_[tinitial:tfinal:tstep]

[7]: #Define derivatives of frames qA,qA_d,qA_dd = Differentiable('qA',system) qB,qB_d,qB_dd = Differentiable('qB',system) qC,qC_d,qC_dd = Differentiable('qC',system) qD,qD_d,qD_dd = Differentiable('qD',system) qE,qE_d,qE_dd = Differentiable('qE',system) qF,qF_d,qF_dd = Differentiable('qF',system) qT,qT_d,qT_dd = Differentiable('qT',system)

x,x_d,x_dd = Differentiable('x',system) y,y_d,y_dd = Differentiable('y',system)

[8]: #set initial conditions
initialvalues = {}
initialvalues[qA]=40*pi/180 initialvalues[qA_d]=0*pi/180 initialvalues[qB]=20*pi/180 initialvalues[qB_d]=0*pi/180 initialvalues[qC]=10*pi/180 initialvalues[qC_d]=0*pi/180 initialvalues[qD]=0*pi/180 initialvalues[qD_d]=0*pi/180 initialvalues[qE]=-10*pi/180 initialvalues[qE_d]=0*pi/180 initialvalues[qF]=-40*pi/180 initialvalues[qF_d]=0*pi/180 initialvalues[qT]=0*pi/180 initialvalues[qT_d]=0*pi/180

initialvalues[x]=0*pi/180
initialvalues[x_d]=0*pi/180 initialvalues[y]=0*pi/180
initialvalues[y_d]=0*pi/180

statevariables = system.get_state_variables()
ini0 = [initialvalues[item] for item in statevariables]

[9]: #Frames
N = Frame('N',system)
A = Frame('A',system)
B = Frame('B',system)
C = Frame('C',system)
D = Frame('D',system)
E = Frame('E',system)
F = Frame('F',system)
T = Frame('T',system)

system.set_newtonian(N)

A.rotate_fixed_axis(N,[0,0,1],qA,system) B.rotate_fixed_axis(N,[0,0,1],qB,system) C.rotate_fixed_axis(N,[0,0,1],qC,system) D.rotate_fixed_axis(N,[0,0,1],qD,system) E.rotate_fixed_axis(N,[0,0,1],qE,system) F.rotate_fixed_axis(N,[0,0,1],qF,system) T.rotate_fixed_axis(N,[0,0,1],qT,system)
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
