AniIOT/Foldable_Robotics_Project/04_Software/03_Anson/Length_Constrained_Dynamics_Optimization_Segment_Area_optimization_ran.pdf

4/21/22, 8:42 AM | Length_Constrained_Dynamics_Optimization_Segment_Area
localhost:8888/nbconvert/html/Downloads/Git/Foldable_Robotics_Project/04_Software/03_Anson/Length_Constrained_Dynamics_Optimization_Seg… | 1/13

# Importing Libraries

### Importing libraries for script

# Constants of System

In this block of code we are defining all the constants of our system that we will use for our

### simulation

In [1]:
%matplotlib inline

In [2]:
#Set script to run optimization run_fit = True

In [3]:
import pynamics
from pynamics.frame import Frame
from pynamics.variable_types import Differentiable,Constant,Variable from pynamics.system import System
from pynamics.body import Body
from pynamics.dyadic import Dyadic
from pynamics.output import Output,PointsOutput
from pynamics.output_points_3d import PointsOutput3D
from pynamics.constraint import AccelerationConstraint,KinematicConstraint from pynamics.particle import Particle
import pynamics.integration
import numpy
import matplotlib.pyplot as plt plt.ion()
from math import pi,sin
import sympy
from sympy import sqrt
import math
import logging
import scipy.optimize
import pynamics.integration import pynamics.system
import numpy.random
import scipy.interpolate
import scipy.optimize
import cma
import pandas as pd
import idealab_tools.units
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
