AniIOT/Foldable_Robotics_Project/01_Documents/04_Presentations/Biomechanics_Background_and_Initial_specifications/Engineering_representation.jpg

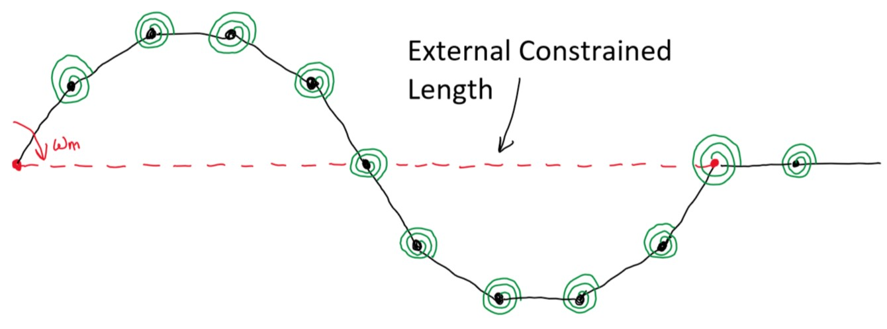
01_Documents/04_Presentations/Biomechanics_Background_and_Initial_specifications/Engineering_representation.jpg
