AniIOT/Foldable_Robotics_Project/01_Documents/04_Presentations/Biomechanics_Background_and_Initial_specifications/Flow_fields_behind_swimming_eels.JPG

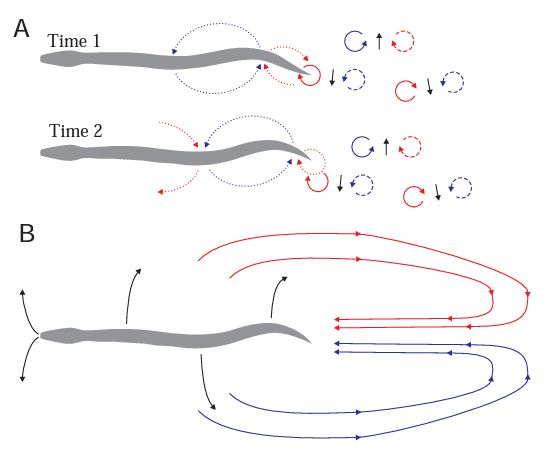
01_Documents/04_Presentations/Biomechanics_Background_and_Initial_specifications/Flow_fields_behind_swimming_eels.JPG
