AniIOT/Foldable_Robotics_Project/01_Documents/04_Presentations/System_Dynamics/Dynamics_2/output_27_1.png

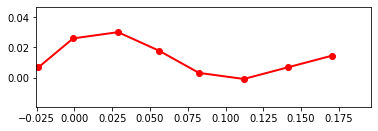
01_Documents/04_Presentations/System_Dynamics/Dynamics_2/output_27_1.png
