AniIOT/Foldable_Robotics_Project/01_Documents/04_Presentations/System_Kinematics/Plot_4.png

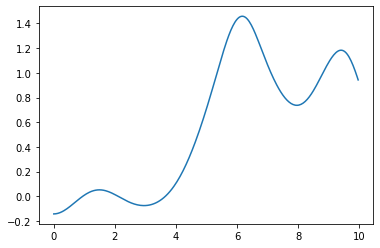
01_Documents/04_Presentations/System_Kinematics/Plot_4.png
