AniIOT/Foldable_Robotics_Project/02_Mechanical/02_CAD/IMG_5580.jpg

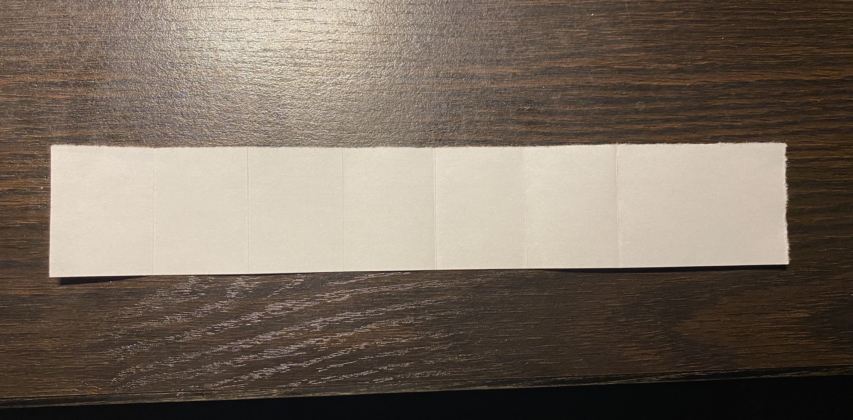
02_Mechanical/02_CAD/IMG_5580.jpg
