AniIOT/Foldable_Robotics_Project/02_Mechanical/02_CAD/IMG_5581.jpg

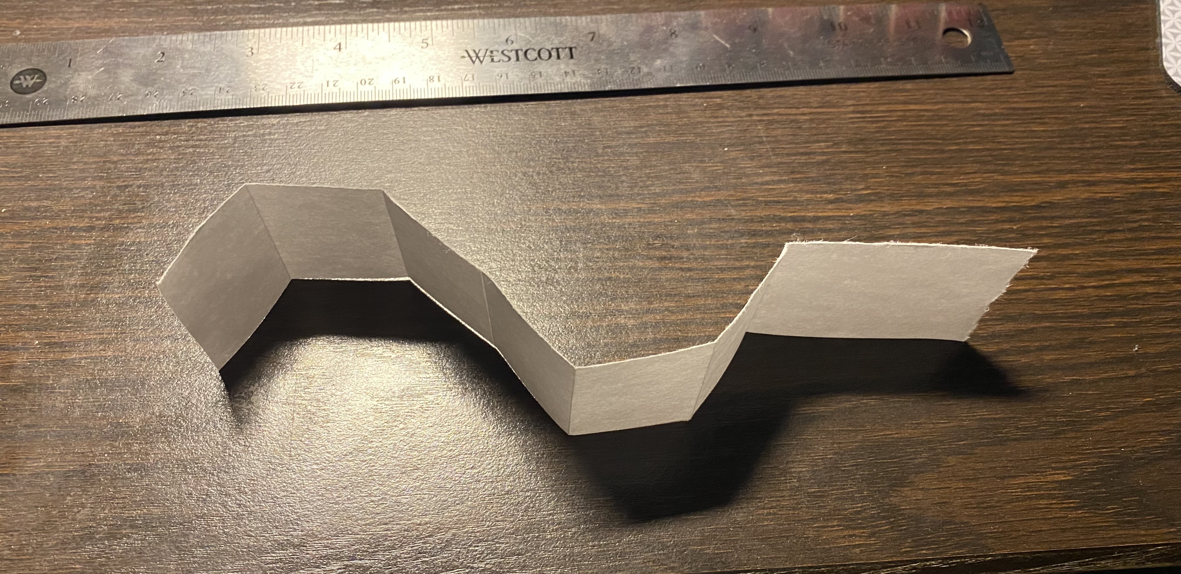
02_Mechanical/02_CAD/IMG_5581.jpg
