AniIOT/Foldable_Robotics_Project/02_Mechanical/02_CAD/Screenshot 2022-04-05 014403.jpg

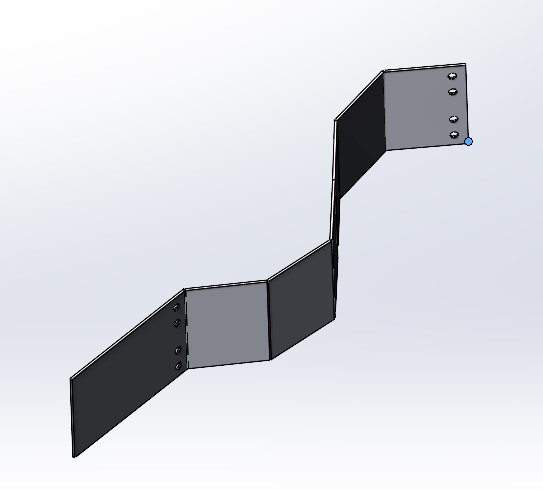
02_Mechanical/02_CAD/Screenshot 2022-04-05 014403.jpg
