AniIOT/Foldable_Robotics_Project/04_Software/03_Anson/CMA vs Actual.png

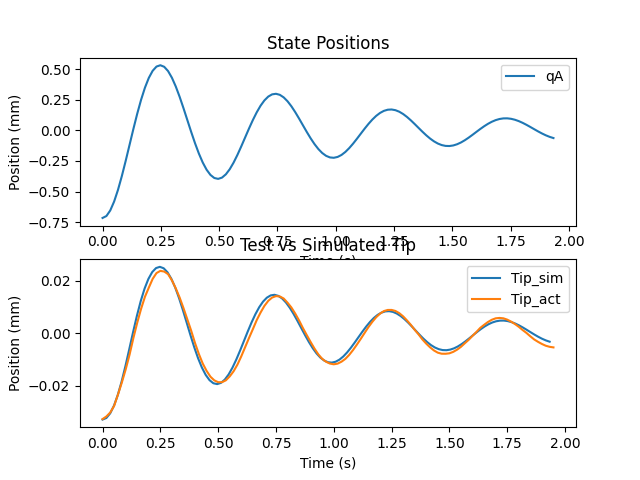
04_Software/03_Anson/CMA vs Actual.png
