AniIOT/Foldable_Robotics_Project/04_Software/03_Anson/CMA_plot.png

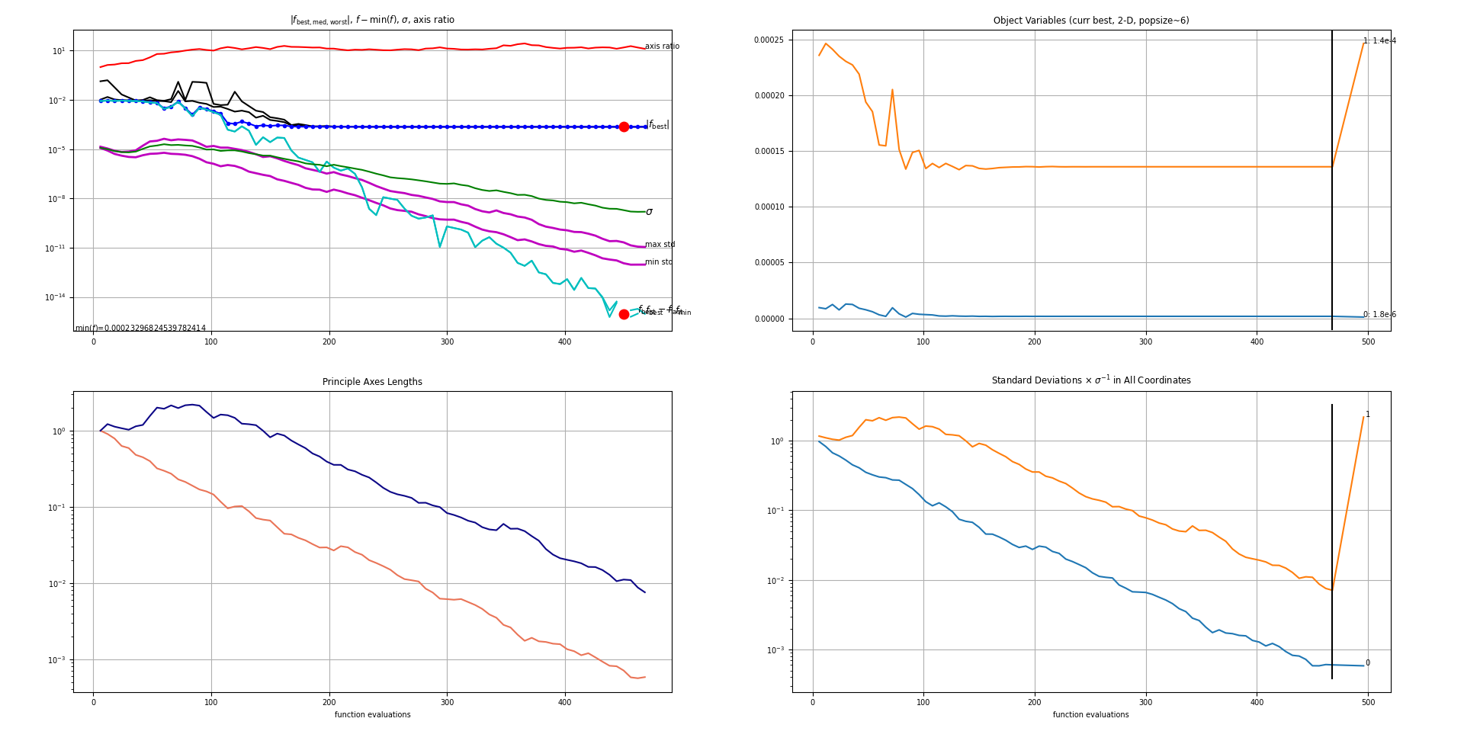
04_Software/03_Anson/CMA_plot.png
