AniIOT/Foldable_Robotics_Project/02_Mechanical/02_CAD/first_pass0.dxf

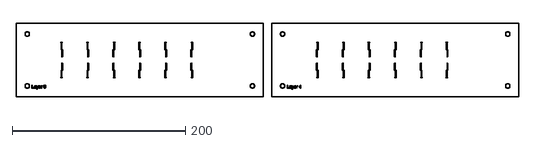
[picture p72: CAD file, 2022-04-05]
02_Mechanical/02_CAD/first_pass0.dxf
579.8 x 84.9
