AniIOT/Foldable_Robotics_Project/02_Mechanical/02_CAD/design.dxf

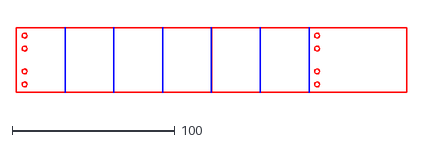
[picture p73: CAD file, 2022-04-05]
02_Mechanical/02_CAD/design.dxf
240.0 x 40.0
