AniIOT/Foldable_Robotics_Project/01_Documents/05_Gallery/Experiments/Damping/Damping_Graph.png

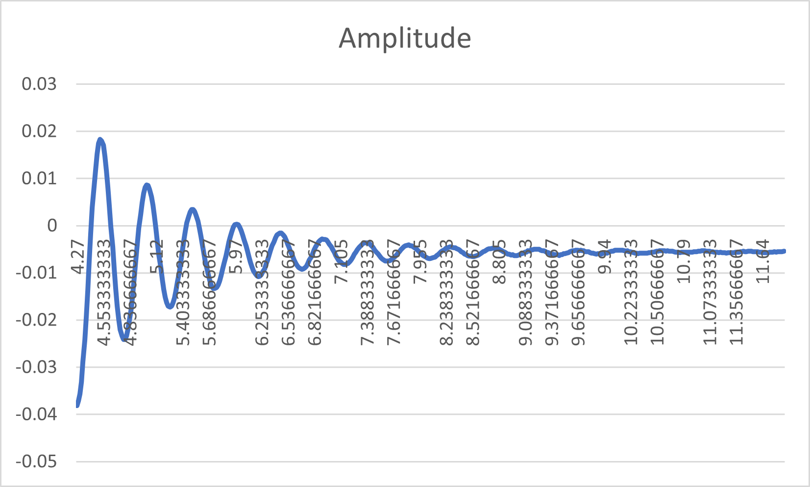
01_Documents/05_Gallery/Experiments/Damping/Damping_Graph.png
