AniIOT/Foldable_Robotics_Project/01_Documents/05_Gallery/Experiments/Damping/Damping_Graph_t0.png

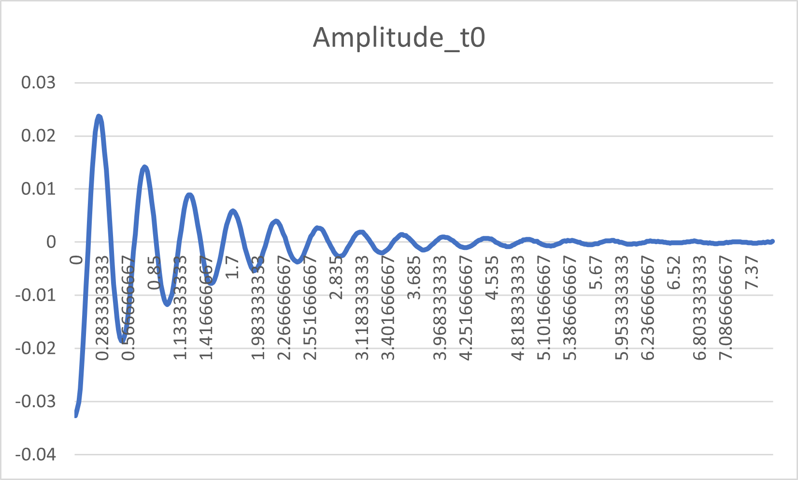
01_Documents/05_Gallery/Experiments/Damping/Damping_Graph_t0.png
