AniIOT/Foldable_Robotics_Project/01_Documents/05_Gallery/Experiments/Damping/Damping_test_1.jpg

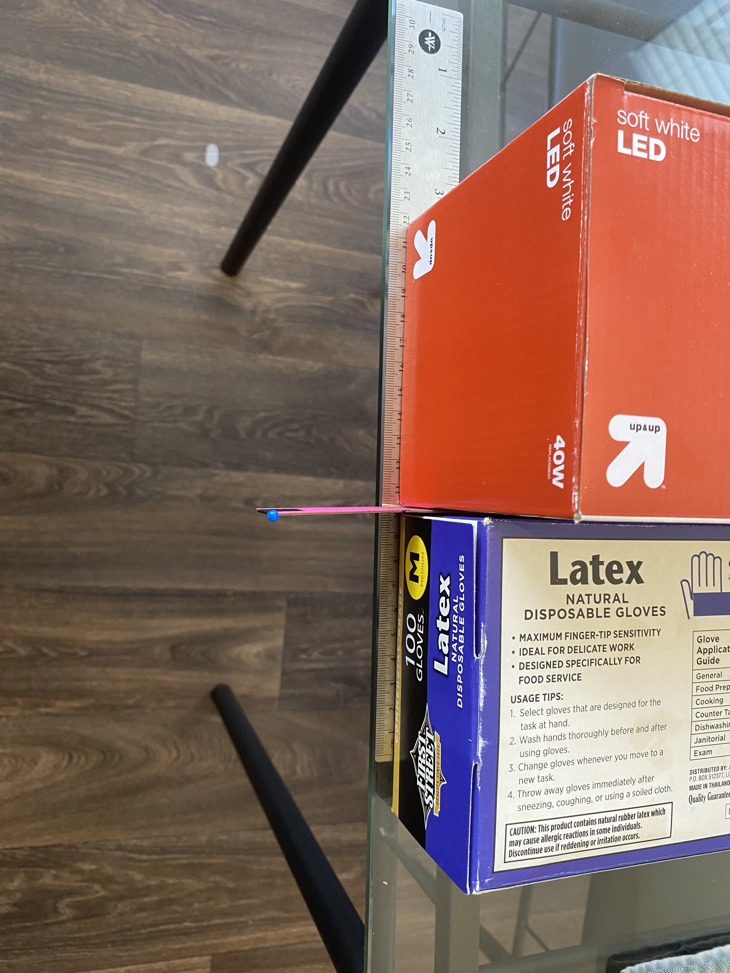
01_Documents/05_Gallery/Experiments/Damping/Damping_test_1.jpg
