AniIOT/Foldable_Robotics_Project/01_Documents/05_Gallery/Experiments/Deflection/Deflection_graph.png

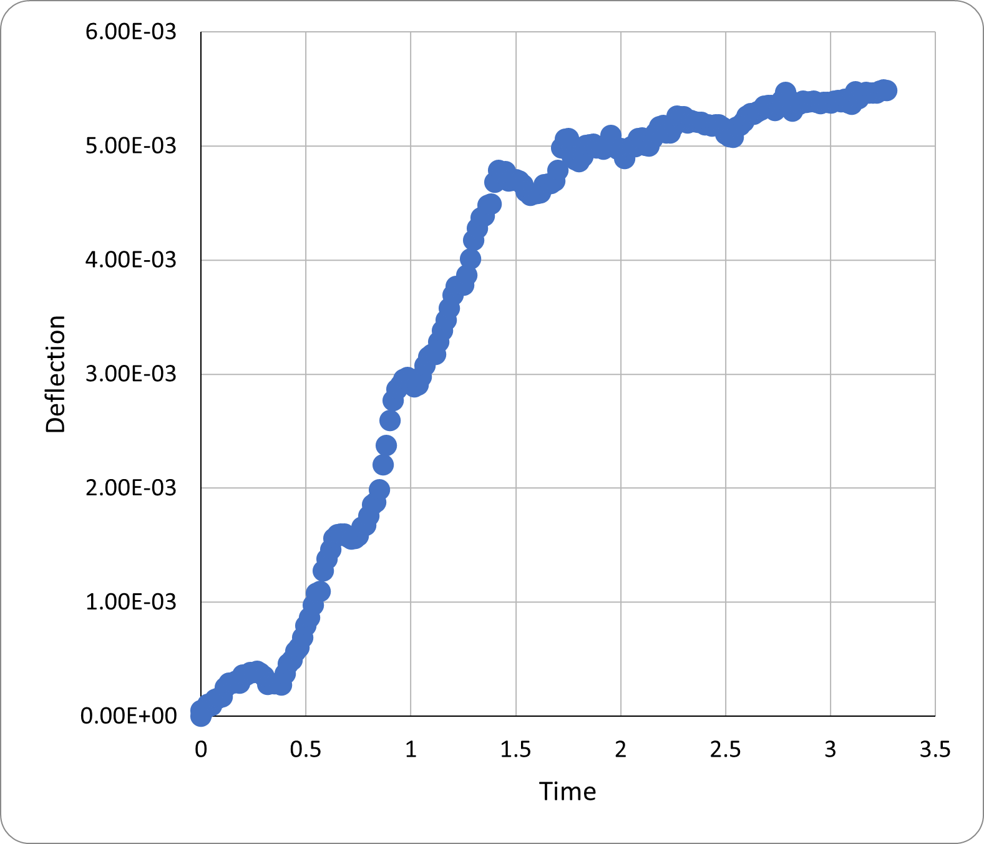
01_Documents/05_Gallery/Experiments/Deflection/Deflection_graph.png
