AniIOT/Foldable_Robotics_Project/04_Software/04_Aniruddha/Tail_Experiment.png

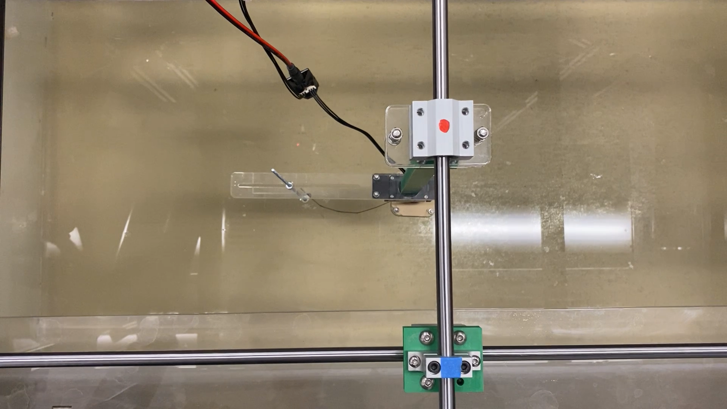
04_Software/04_Aniruddha/Tail_Experiment.png
